ggrummer/Starlite/SolRadi/instr_dpram_sect0/testbench/dut_params.v

localparam FAMILY = "iCE40UP";
localparam MEM_ID = "instr_dpram_sect0";
localparam MEM_SIZE = "32,256";
localparam WADDR_DEPTH = 256;
localparam WDATA_WIDTH = 32;
localparam RADDR_DEPTH = 256;
localparam RDATA_WIDTH = 32;
localparam WADDR_WIDTH = 8;
localparam REGMODE = "noreg";
localparam RADDR_WIDTH = 8;
localparam OUTPUT_CLK_EN = 0;
localparam RESETMODE = "sync";
localparam BYTE_ENABLE = 0;
localparam BYTE_WIDTH = 1;
localparam BYTE_SIZE = 8;
localparam ECC_ENABLE = 0;
localparam INIT_MODE = "mem_file";
localparam INIT_FILE = "C:/Projects/Starlite/SolRadi/instr_dpram_sect0/misc/spiral_instr_dpram_sect0_copy.mem";
localparam INIT_FILE_FORMAT = "hex";
localparam INIT_VALUE_00 = "0x000020008FF0500012004062405240424032402240124002A0000000B00070000x000000009000100000008F0F9F004FB040F060BFB03FF00F1000000000000000";
localparam INIT_VALUE_01 = "0x00000000000000000000000000000000000000000000000000000000000000000x0000000000000000000000000000000000000000000000000000000000000000";
localparam INIT_VALUE_02 = "0x00000000000000000000000000000000000000000000000000000000000000000x0000000000000000000000000000000000000000000000000000000000000000";
localparam INIT_VALUE_03 = "0x00000000000000000000000000000000000000000000000000000000000000000x0000000000000000000000000000000000000000000000000000000000000000";
localparam INIT_VALUE_04 = "0x00000000000000000000000000000000000000000000000000000000000000000x0000000000000000000000000000000000000000000000000000000000000000";
localparam INIT_VALUE_05 = "0x00000000000000000000000000000000000000000000000000000000000000000x0000000000000000000000000000000000000000000000000000000000000000";
localparam INIT_VALUE_06 = "0x00000000000000000000000000000000000000000000000000000000000000000x0000000000000000000000000000000000000000000000000000000000000000";
localparam INIT_VALUE_07 = "0x00000000000000000000000000000000000000000000000000000000000000000x0000000000000000000000000000000000000000000000000000000000000000";
localparam INIT_VALUE_08 = "0x00000000000000000000000000000000000000000000000000000000000000000x0000000000000000000000000000000000000000000000000000000000000000";
localparam INIT_VALUE_09 = "0x00000000000000000000000000000000000000000000000000000000000000000x0000000000000000000000000000000000000000000000000000000000000000";
localparam INIT_VALUE_0A = "0x00000000000000000000000000000000000000000000000000000000000000000x0000000000000000000000000000000000000000000000000000000000000000";
localparam INIT_VALUE_0B = "0x00000000000000000000000000000000000000000000000000000000000000000x0000000000000000000000000000000000000000000000000000000000000000";
localparam INIT_VALUE_0C = "0x00000000000000000000000000000000000000000000000000000000000000000x0000000000000000000000000000000000000000000000000000000000000000";
localparam INIT_VALUE_0D = "0x00000000000000000000000000000000000000000000000000000000000000000x0000000000000000000000000000000000000000000000000000000000000000";
localparam INIT_VALUE_0E = "0x00000000000000000000000000000000000000000000000000000000000000000x0000000000000000000000000000000000000000000000000000000000000000";
localparam INIT_VALUE_0F = "0x00000000000000000000000000000000000000000000000000000000000000000x0000000000000000000000000000000000000000000000000000000000000000";
localparam INIT_VALUE_10 = "0x0000000000000000000000000000000000000000000000000000000000000000";
localparam INIT_VALUE_11 = "0x0000000000000000000000000000000000000000000000000000000000000000";
localparam INIT_VALUE_12 = "0x0000000000000000000000000000000000000000000000000000000000000000";
localparam INIT_VALUE_13 = "0x0000000000000000000000000000000000000000000000000000000000000000";
localparam INIT_VALUE_14 = "0x0000000000000000000000000000000000000000000000000000000000000000";
localparam INIT_VALUE_15 = "0x0000000000000000000000000000000000000000000000000000000000000000";
localparam INIT_VALUE_16 = "0x0000000000000000000000000000000000000000000000000000000000000000";
localparam INIT_VALUE_17 = "0x0000000000000000000000000000000000000000000000000000000000000000";
localparam INIT_VALUE_18 = "0x0000000000000000000000000000000000000000000000000000000000000000";
localparam INIT_VALUE_19 = "0x0000000000000000000000000000000000000000000000000000000000000000";
localparam INIT_VALUE_1A = "0x0000000000000000000000000000000000000000000000000000000000000000";
localparam INIT_VALUE_1B = "0x0000000000000000000000000000000000000000000000000000000000000000";
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
localparam INIT_VALUE_3E = "0x0000000000000000000000000000000000000000000000000000000000000000";
localparam INIT_VALUE_3F = "0x0000000000000000000000000000000000000000000000000000000000000000";
`define iCE40UP
`define ice40tp
`define iCE40UP5K
