ggrummer/Starlite/SolUP12/rtl/PLL_pad/SolUP12_pll_inst.v

SolUP12_pll SolUP12_pll_inst(.PACKAGEPIN(),
                             .PLLOUTCORE(),
                             .PLLOUTGLOBAL(),
                             .RESET(),
                             .LOCK());
