ggrummer/Starlite/SolUP12/rtl/SolUP12_pll_inst.v

SolUP12_pll SolUP12_pll_inst(.REFERENCECLK(),
                             .PLLOUTCORE(),
                             .PLLOUTGLOBAL(),
                             .RESET(),
                             .LOCK());
